andruhon/super-custom-keycaps/keycaps-default-one-material.scad

include <keycaps-default-all.scad>;

TO_RENDER = "body";
AUTO_LAYOUT = true;
AUTO_LAYOUT_KEYS_PER_ROW = 6;
