andruhon/super-custom-keycaps/keycaps-default-right.scad

include <keycaps-default-all.scad>;

SIDE = "right";
