andruhon/super-custom-keycaps/keycaps-default-side-unfilled.scad

include <keycaps-default-all.scad>;

AUTO_LAYOUT = true;
AUTO_LAYOUT_KEYS_PER_ROW = 6;
SIDE_FILL = false;
