andruhon/super-custom-keycaps/keycaps-default-verbose.scad

include <keycaps-default-all.scad>;

VERBOSE_LABELS = true;
